Daiki51/yamaken-music-player/src/YamakenMusicPlayer/urlencode.h

/*
 ESP8266 Hello World urlencode by Steve Nelson
 URLEncoding is used all the time with internet urls. This is how urls handle funny characters
 in a URL. For example a space is: %20
 These functions simplify the process of encoding and decoding the urlencoded format.
  
 It has been tested on an esp12e (NodeMCU development board)
 This example code is in the public domain, use it however you want. 
  Prerequisite Examples:
  https://github.com/zenmanenergy/ESP8266-Arduino-Examples/tree/master/helloworld_serial
*/
unsigned char h2int(char c);

String urldecode(String str)
{
    
    String encodedString="";
    char c;
    char code0;
    char code1;
    for (int i =0; i < str.length(); i++){
        c=str.charAt(i);
      if (c == '+'){
        encodedString+=' ';  
      }else if (c == '%') {
        i++;
        code0=str.charAt(i);
        i++;
        code1=str.charAt(i);
        c = (h2int(code0) << 4) | h2int(code1);
        encodedString+=c;
      } else{
        
        encodedString+=c;  
      }
      
      yield();
    }
    
   return encodedString;
}

String urlencode(String str)
{
    String encodedString="";
    char c;
    char code0;
    char code1;
    char code2;
    for (int i =0; i < str.length(); i++){
      c=str.charAt(i);
      if (c == ' '){
        encodedString+= '+';
      } else if (isalnum(c)){
        encodedString+=c;
      } else{
        code1=(c & 0xf)+'0';
        if ((c & 0xf) >9){
            code1=(c & 0xf) - 10 + 'A';
        }
        c=(c>>4)&0xf;
        code0=c+'0';
        if (c > 9){
            code0=c - 10 + 'A';
        }
        code2='\0';
        encodedString+='%';
        encodedString+=code0;
        encodedString+=code1;
        //encodedString+=code2;
      }
      yield();
    }
    return encodedString;
    
}

unsigned char h2int(char c)
{
    if (c >= '0' && c <='9'){
        return((unsigned char)c - '0');
    }
    if (c >= 'a' && c <='f'){
        return((unsigned char)c - 'a' + 10);
    }
    if (c >= 'A' && c <='F'){
        return((unsigned char)c - 'A' + 10);
    }
    return(0);
}
